mikelawrence/esphome-indoor-multi-sensor-hardware/enclosure/3d-printing/Corner-Mount/ESPHome-Indoor-Multi-Sensor-Corner-Back-Mount-Gasket.step

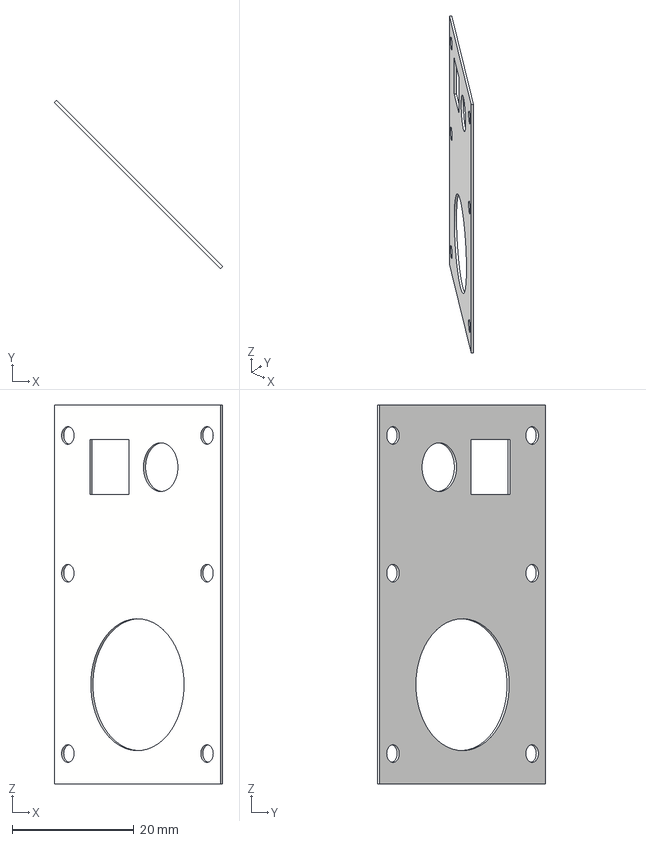
[picture p21: CAD file, 2025-10-03]
enclosure/3d-printing/Corner-Mount/ESPHome-Indoor-Multi-Sensor-Corner-Back-Mount-Gasket.step
27.6 x 27.6 x 62.2 mm
