mikelawrence/esphome-indoor-multi-sensor-hardware/enclosure/3d-printing/Angle-Wallplate/ESPHome-Indoor-Multi-Sensor-Angle-Wallplate-Left-Facing-SEN66.step

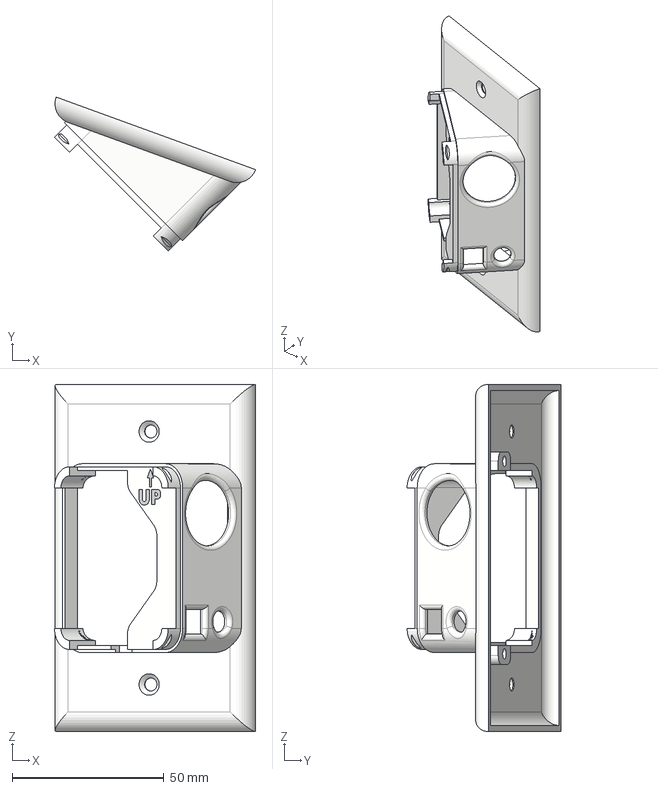
[picture p22: CAD file, 2025-10-01]
enclosure/3d-printing/Angle-Wallplate/ESPHome-Indoor-Multi-Sensor-Angle-Wallplate-Left-Facing-SEN66.step
66.2 x 50.7 x 114.3 mm
