mikelawrence/esphome-indoor-multi-sensor-hardware/enclosure/3d-printing/Corner-Mount/ESPHome-Indoor-Multi-Sensor-Corner-Back-Mount-5°.step

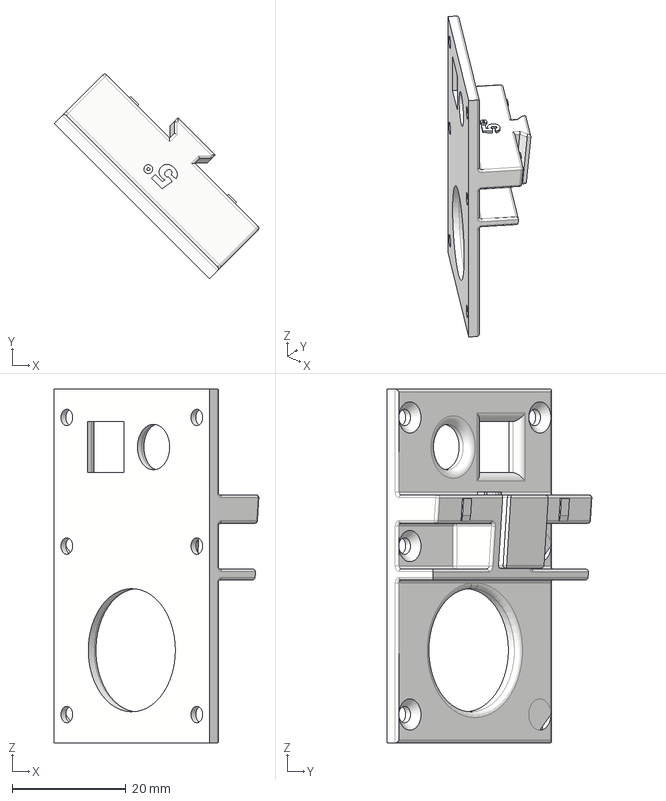
[picture p23: CAD file, 2025-10-03]
enclosure/3d-printing/Corner-Mount/ESPHome-Indoor-Multi-Sensor-Corner-Back-Mount-5°.step
36.0 x 36.0 x 62.2 mm
