mikelawrence/esphome-indoor-multi-sensor-hardware/pcb/3dmodels/User Library-TGS5141.STEP

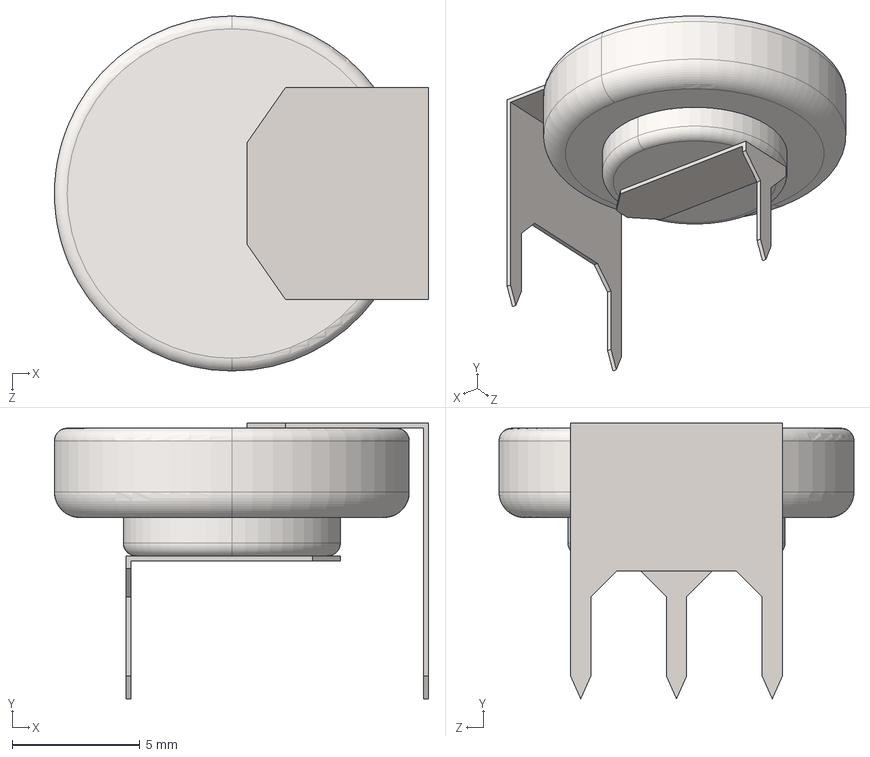
[picture p24: CAD file, 2025-07-08]
pcb/3dmodels/User Library-TGS5141.STEP
14.6 x 10.8 x 13.9 mm
