mikelawrence/esphome-indoor-multi-sensor-hardware/enclosure/3d-printing/Angle-Wallplate/ESPHome-Indoor-Multi-Sensor-Angle-Wallplate-Right-Facing-SEN66.step

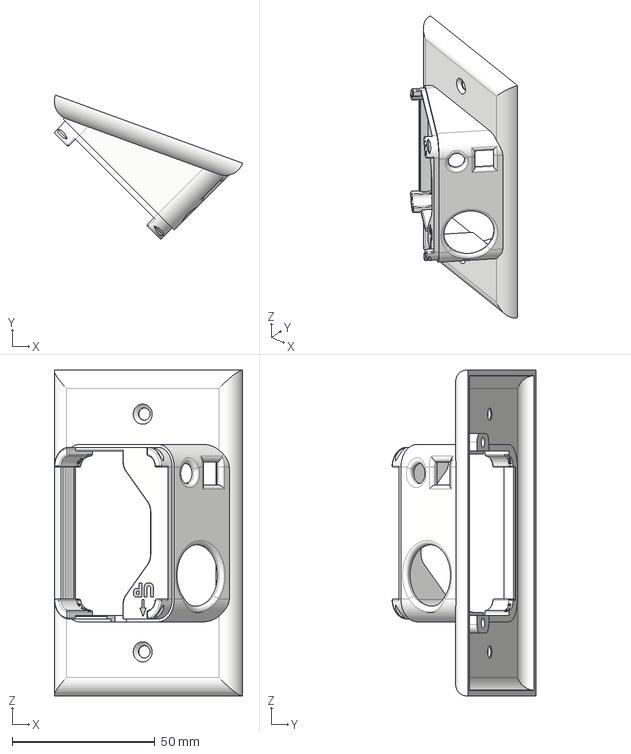
[picture p25: CAD file, 2025-10-01]
enclosure/3d-printing/Angle-Wallplate/ESPHome-Indoor-Multi-Sensor-Angle-Wallplate-Right-Facing-SEN66.step
66.0 x 50.4 x 114.3 mm
