mikelawrence/esphome-indoor-multi-sensor-hardware/enclosure/3d-printing/Corner-Mount/ESPHome-Indoor-Multi-Sensor-Corner-Corner-Mount-25°.step

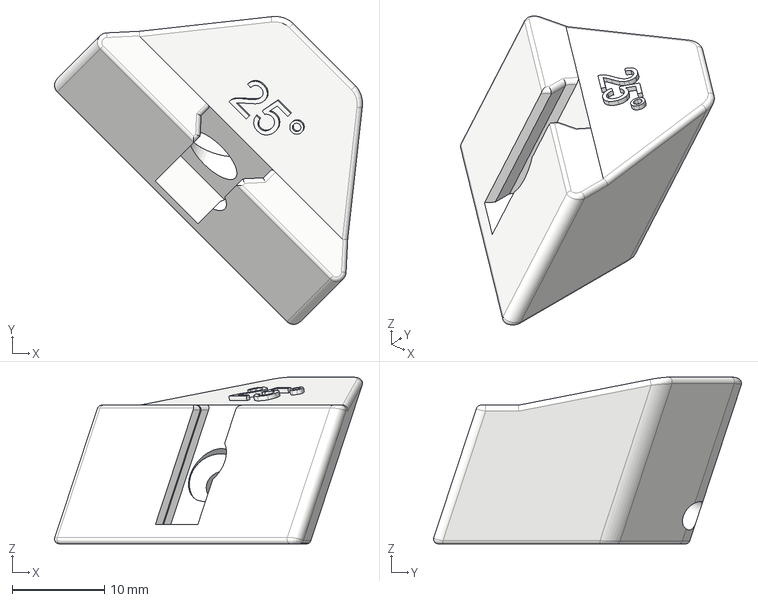
[picture p26: CAD file, 2025-10-03]
enclosure/3d-printing/Corner-Mount/ESPHome-Indoor-Multi-Sensor-Corner-Corner-Mount-25°.step
33.3 x 33.3 x 18.0 mm
