mikelawrence/esphome-indoor-multi-sensor-hardware/enclosure/3d-printing/Corner-Mount/ESPHome-Indoor-Multi-Sensor-Corner-Back-Mount-15°.step

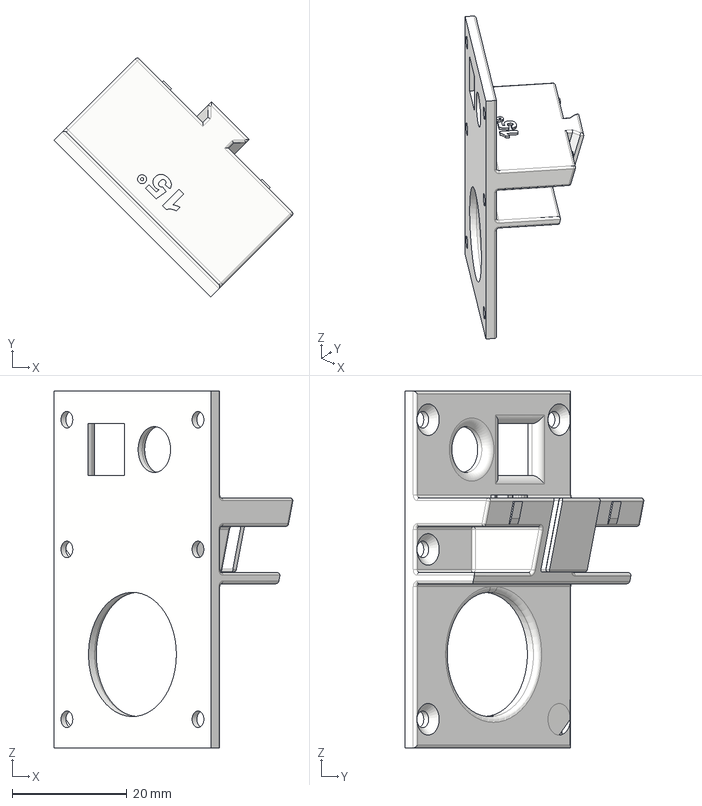
[picture p27: CAD file, 2025-10-03]
enclosure/3d-printing/Corner-Mount/ESPHome-Indoor-Multi-Sensor-Corner-Back-Mount-15°.step
41.6 x 41.6 x 62.2 mm
