mikelawrence/esphome-indoor-multi-sensor-hardware/enclosure/3d-printing/Angle-Wallplate/ESPHome-Indoor-Multi-Sensor-Angle-Wallplate-Speaker-Enclosure.step

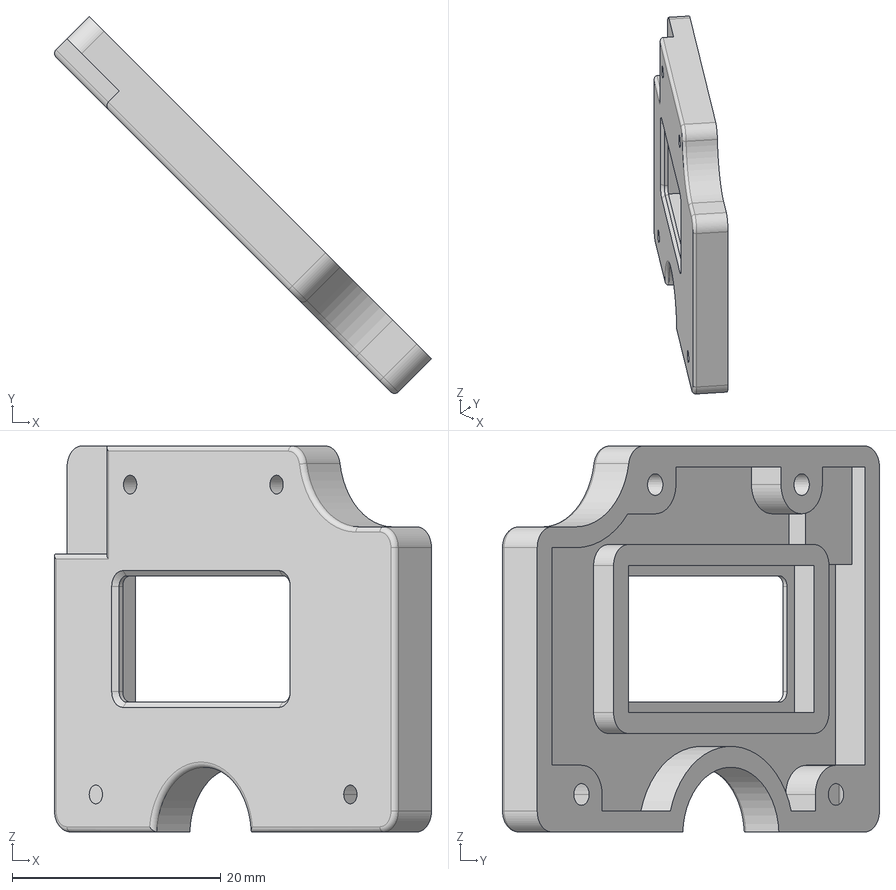
[picture p28: CAD file, 2025-10-01]
enclosure/3d-printing/Angle-Wallplate/ESPHome-Indoor-Multi-Sensor-Angle-Wallplate-Speaker-Enclosure.step
36.1 x 36.1 x 37.0 mm
