mikelawrence/esphome-indoor-multi-sensor-hardware/enclosure/3d-printing/Corner-Mount/ESPHome-Indoor-Multi-Sensor-Corner-Corner-Mount-15°.step

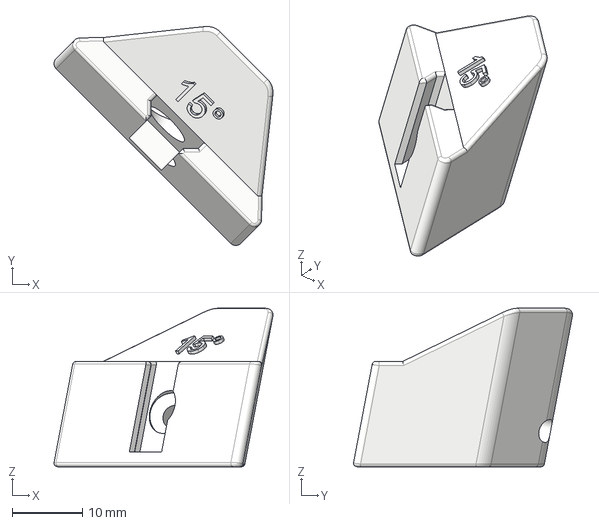
[picture p29: CAD file, 2025-10-03]
enclosure/3d-printing/Corner-Mount/ESPHome-Indoor-Multi-Sensor-Corner-Corner-Mount-15°.step
31.2 x 31.2 x 22.6 mm
