mikelawrence/esphome-indoor-multi-sensor-hardware/enclosure/3d-printing/Angle-Wallplate/ESPHome-Indoor-Multi-Sensor-Angle-Wallplate-Cap-SEN66.step

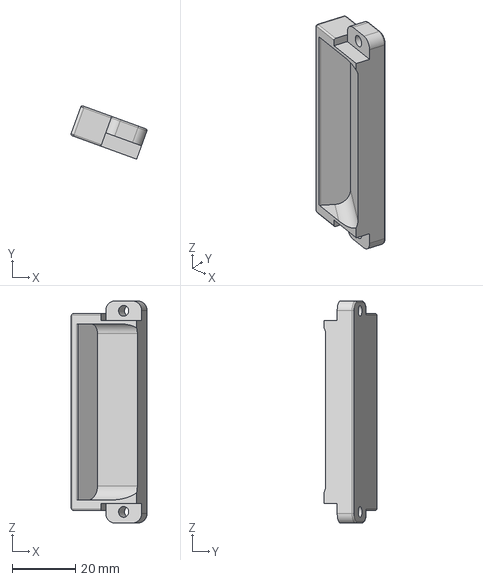
[picture p30: CAD file, 2025-10-01]
enclosure/3d-printing/Angle-Wallplate/ESPHome-Indoor-Multi-Sensor-Angle-Wallplate-Cap-SEN66.step
24.0 x 16.8 x 70.0 mm
