mikelawrence/esphome-indoor-multi-sensor-hardware/enclosure/3d-printing/Angle-Wallplate/ESPHome-Indoor-Multi-Sensor-Angle-Wallplate-Speaker-Enclosure-Gasket.step

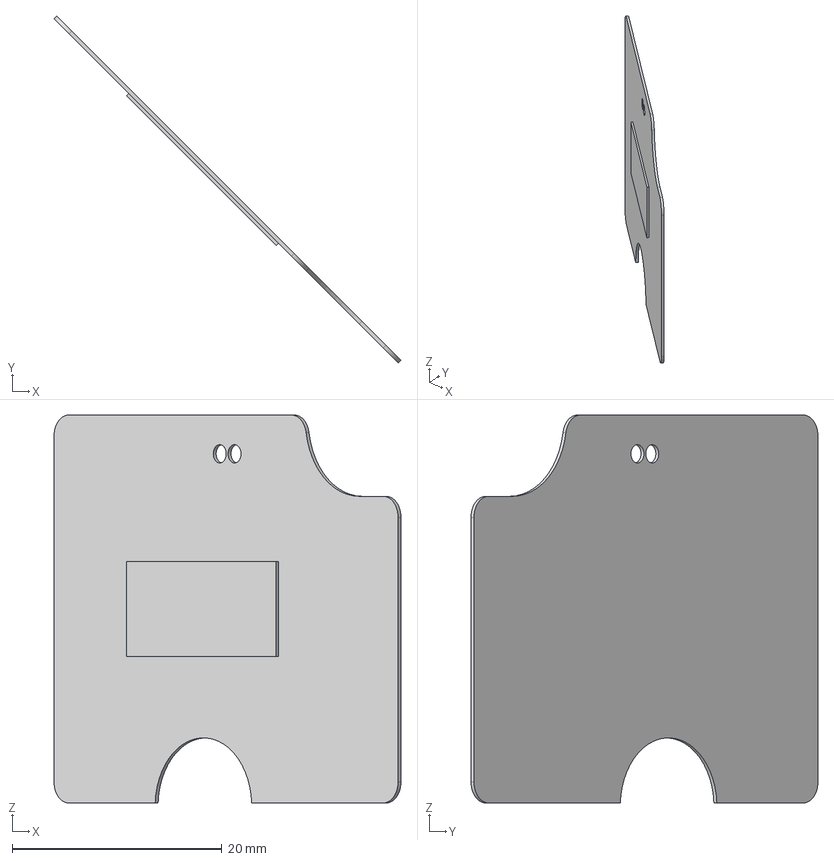
[picture p32: CAD file, 2025-10-01]
enclosure/3d-printing/Angle-Wallplate/ESPHome-Indoor-Multi-Sensor-Angle-Wallplate-Speaker-Enclosure-Gasket.step
33.1 x 33.1 x 37.0 mm
