mikelawrence/esphome-indoor-multi-sensor-hardware/pcb/3dmodels/Same_Sky_CMS-321437-24SP-X8.step

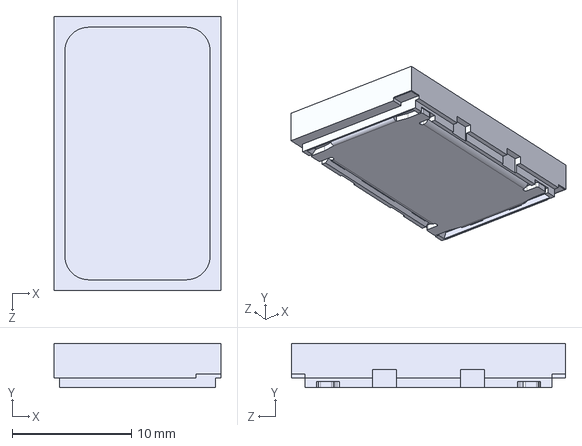
[picture p34: CAD file, 2025-07-08]
pcb/3dmodels/Same_Sky_CMS-321437-24SP-X8.step
14.0 x 3.70 x 23.0 mm
