mikelawrence/esphome-indoor-multi-sensor-hardware/pcb/3dmodels/SHT45-AD1B-R2--3DModel-STEP-369182.STEP

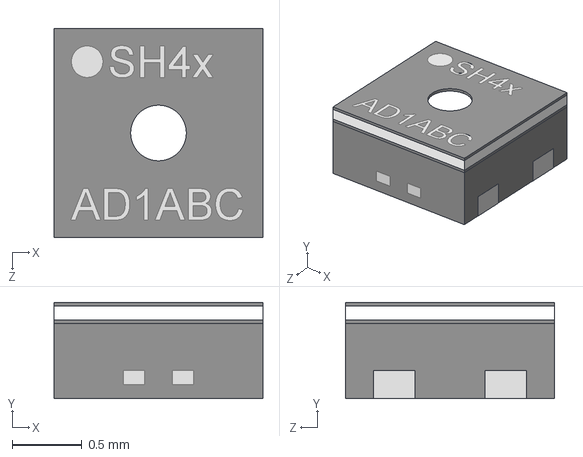
[picture p39: CAD file, 2025-07-08]
pcb/3dmodels/SHT45-AD1B-R2--3DModel-STEP-369182.STEP
1.50 x 0.691 x 1.50 mm
