mikelawrence/esphome-indoor-multi-sensor-hardware/pcb/3dmodels/CES-105-01-T-S.stp

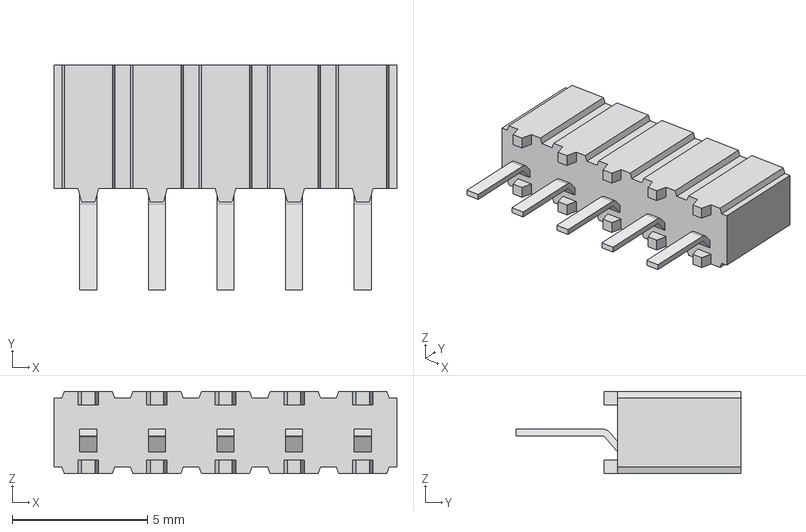
[picture p41: CAD file, 2025-07-08]
pcb/3dmodels/CES-105-01-T-S.stp
12.7 x 8.33 x 3.05 mm
CES-105-01-S_socket
010501TS
010501TS2
