mikelawrence/esphome-indoor-multi-sensor-hardware/pcb/3dmodels/ast-ind-250605.STEP

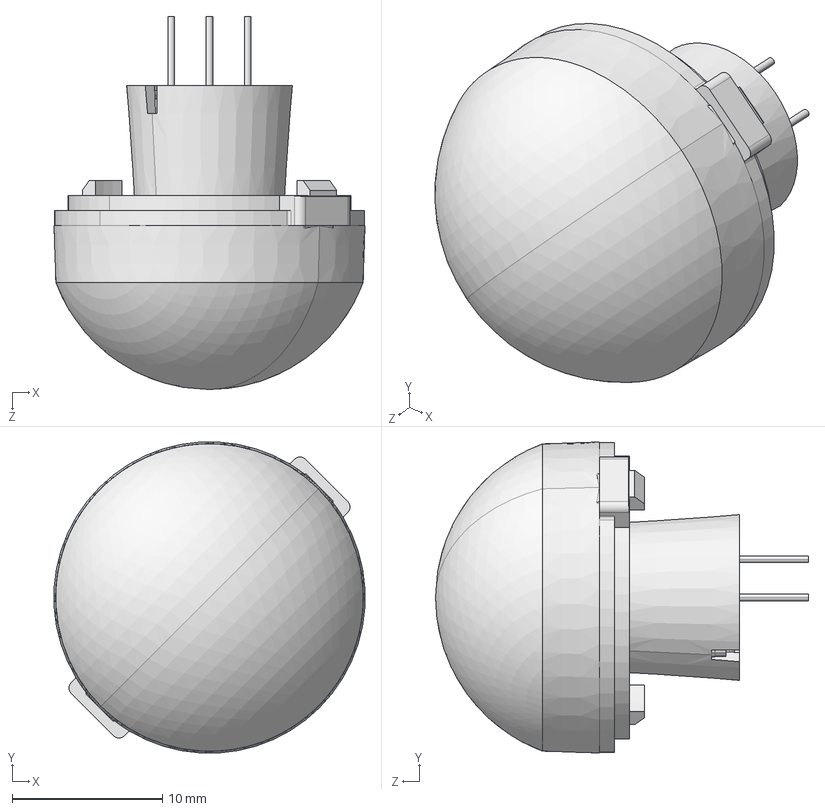
[picture p42: CAD file, 2025-07-08]
pcb/3dmodels/ast-ind-250605.STEP
20.7 x 20.7 x 24.8 mm
