mikelawrence/esphome-indoor-multi-sensor-hardware/pcb/3dmodels/WS2812-2020--3DModel-STEP-1.STEP

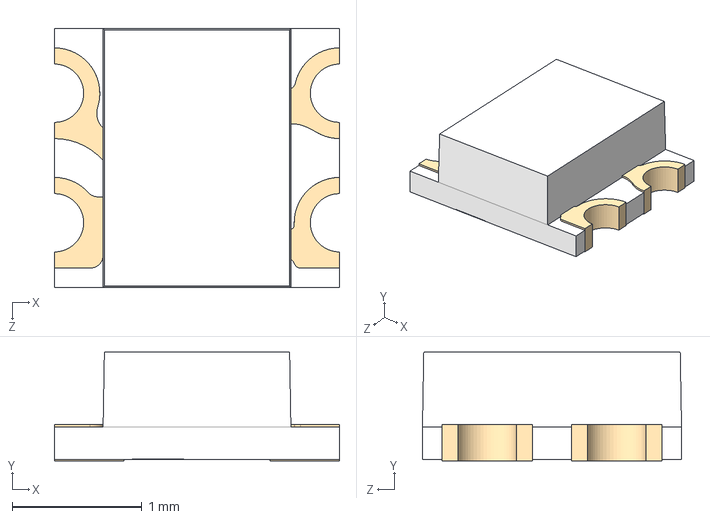
[picture p43: CAD file, 2025-07-08]
pcb/3dmodels/WS2812-2020--3DModel-STEP-1.STEP
2.20 x 0.84 x 2.00 mm
