mikelawrence/esphome-indoor-multi-sensor-hardware/pcb/3dmodels/ESP32-S3-MINI-1-N8--3DModel-STEP-1.STEP

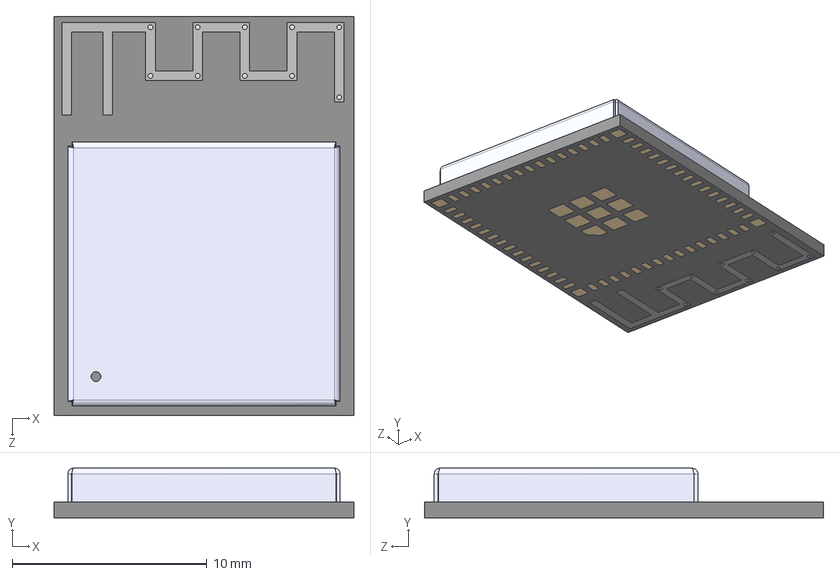
[picture p45: CAD file, 2025-07-08]
pcb/3dmodels/ESP32-S3-MINI-1-N8--3DModel-STEP-1.STEP
15.4 x 2.55 x 20.5 mm
