mikelawrence/esphome-indoor-multi-sensor-hardware/pcb/3dmodels/DW-05-08-T-S-250.stp

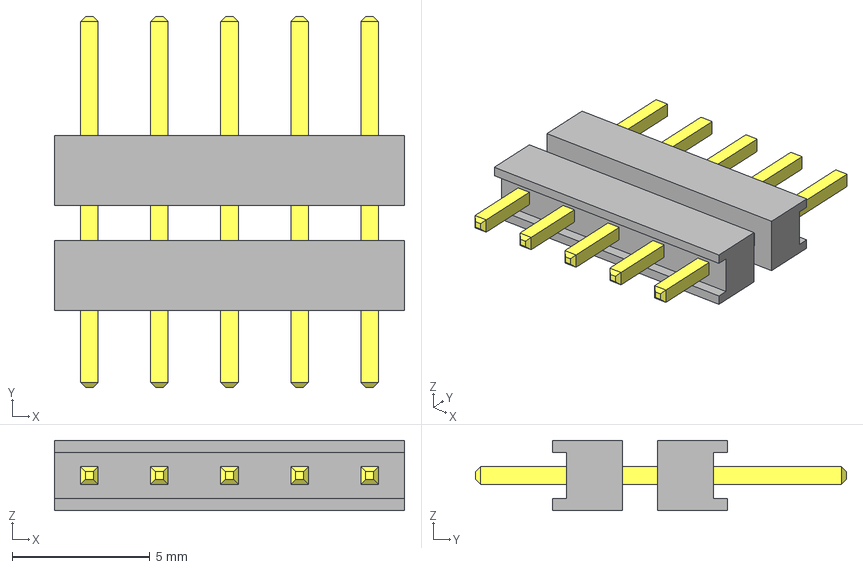
[picture p46: CAD file, 2025-07-08]
pcb/3dmodels/DW-05-08-T-S-250.stp
12.7 x 13.5 x 2.54 mm
ZW-05-08-G-S-250-110bbody
ZW-05-08-G-S-250-110_pins
ZW-05-08-G-S-250-110_top_body
