mikelawrence/esphome-indoor-multi-sensor-hardware/pcb/3dmodels/TLW-105-06-T-S.stp

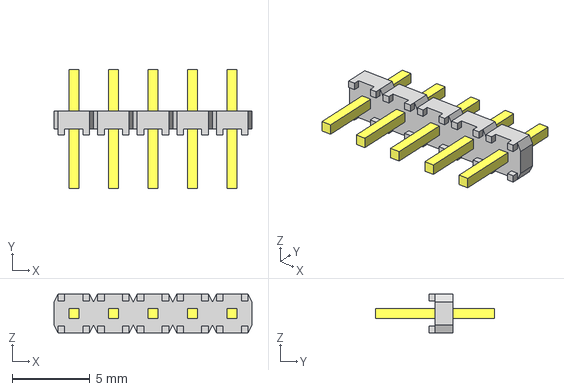
[picture p47: CAD file, 2025-07-08]
pcb/3dmodels/TLW-105-06-T-S.stp
12.7 x 7.62 x 2.49 mm
TLW-105-06-T-S_terminal
TLW-05-06-S0.3
