mikelawrence/esphome-indoor-multi-sensor-hardware/pcb/3dmodels/HLK-2410B.step

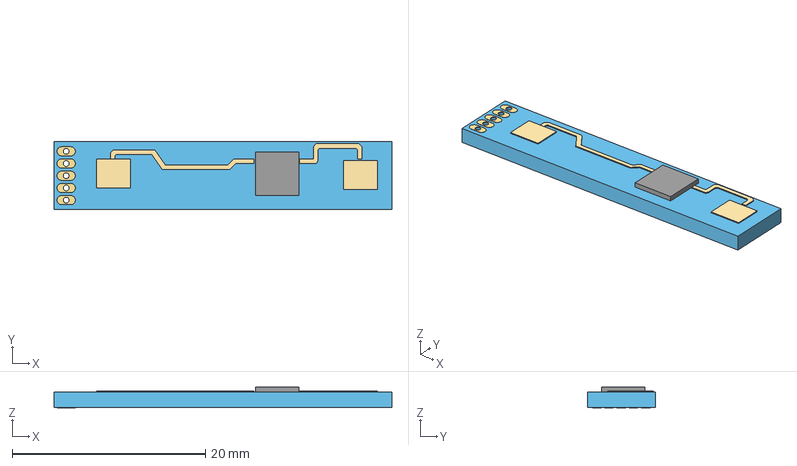
[picture p48: CAD file, 2025-07-08]
pcb/3dmodels/HLK-2410B.step
35.0 x 7.00 x 2.15 mm
